samowitsch/raspberry-pi-hq-microscope/pics/pcb/pcb-back.jpg

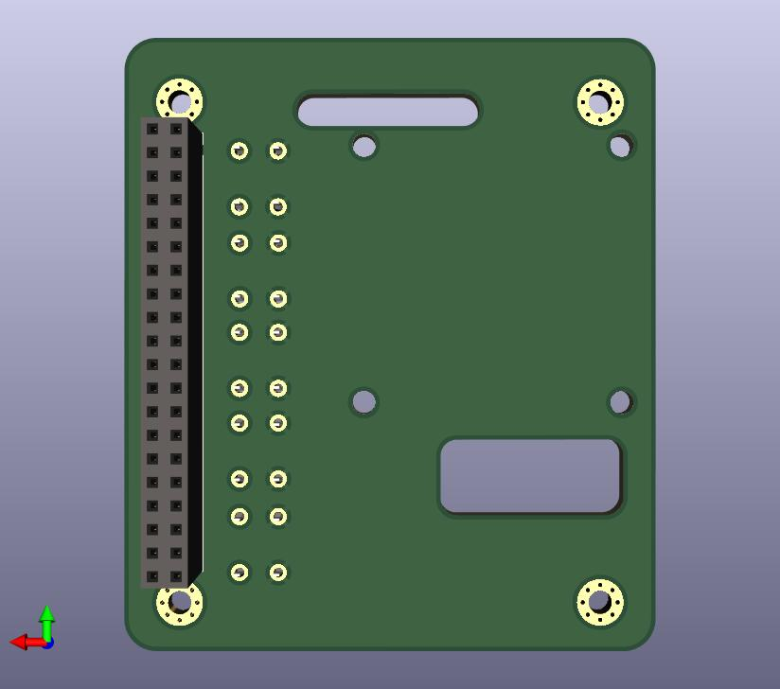
pics/pcb/pcb-back.jpg
