samowitsch/raspberry-pi-hq-microscope/pics/pcb/pcb-front.jpg

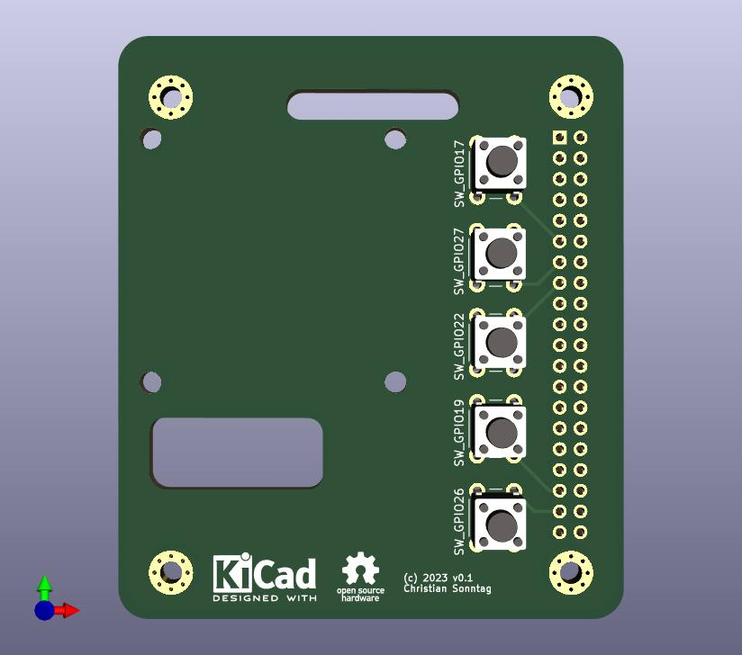
pics/pcb/pcb-front.jpg
