samowitsch/raspberry-pi-hq-microscope/scans/scan-rpi-3a+-case-1-1.png

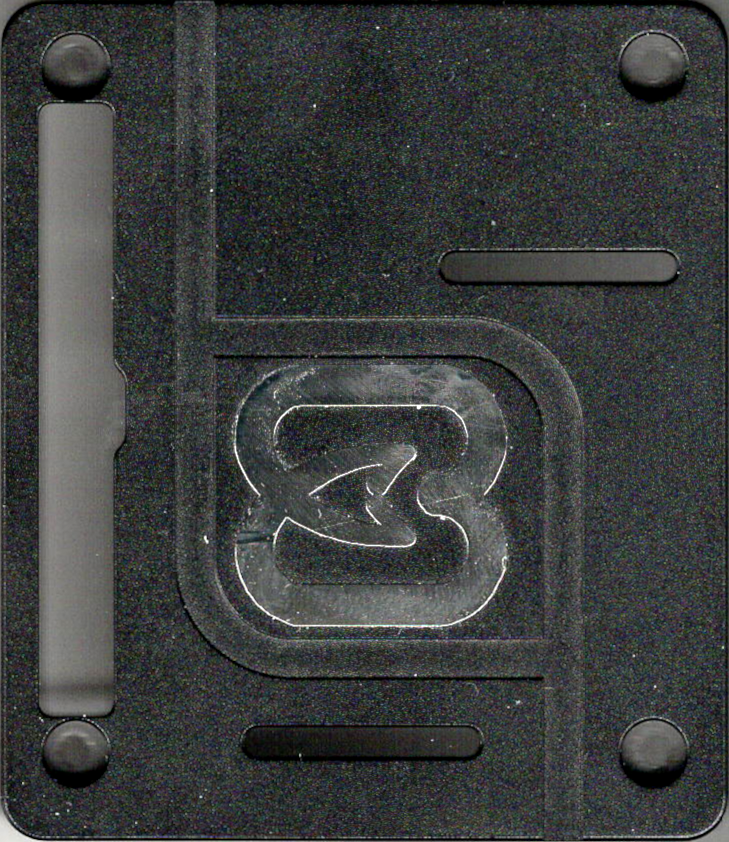
scans/scan-rpi-3a+-case-1-1.png
