samowitsch/raspberry-pi-hq-microscope/scans/scan-rpi-hq-camera-1-1.png

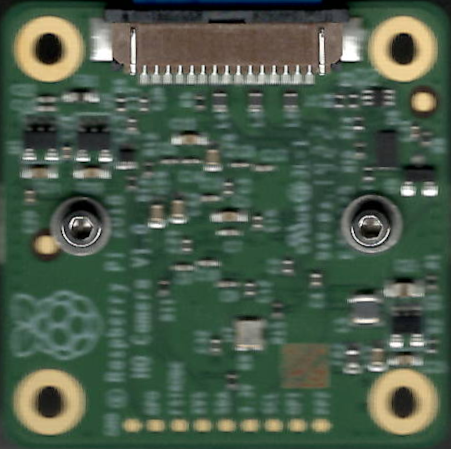
scans/scan-rpi-hq-camera-1-1.png
