samowitsch/raspberry-pi-hq-microscope/pics/bom/edimax-usb-wifi.jpg

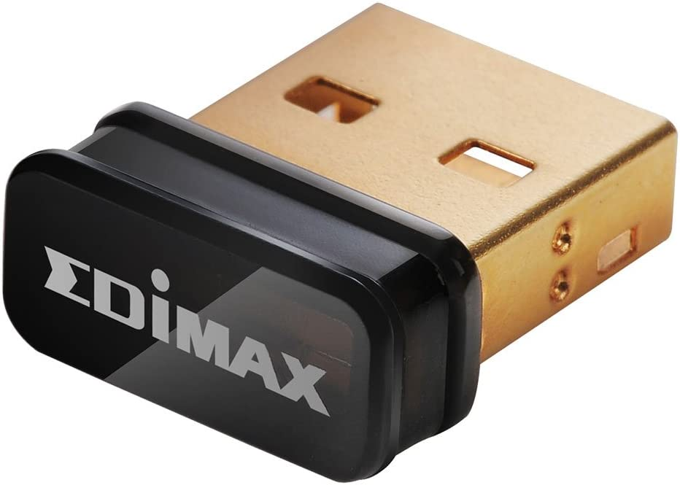
pics/bom/edimax-usb-wifi.jpg
