samowitsch/raspberry-pi-hq-microscope/pics/bom/geekworm-rpi-3a-plus-case.jpg

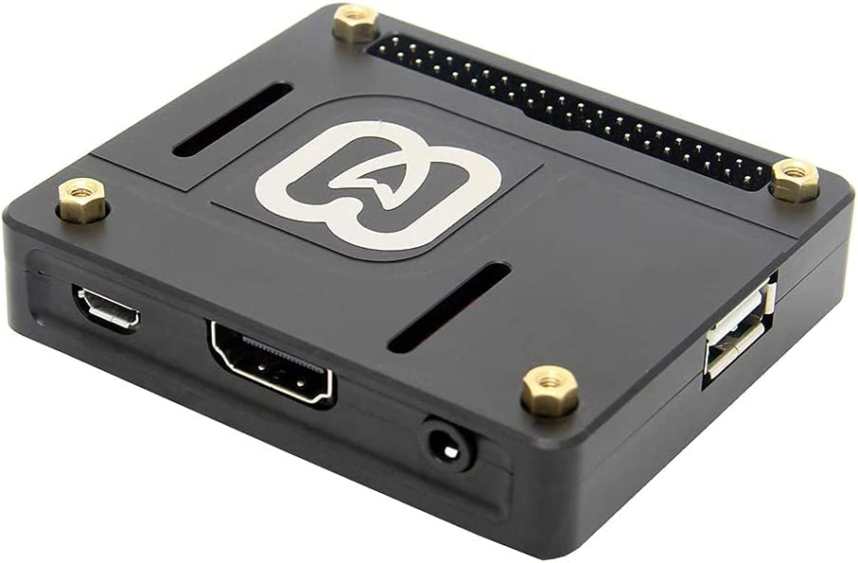
pics/bom/geekworm-rpi-3a-plus-case.jpg
