samowitsch/raspberry-pi-hq-microscope/pics/bom/led-ring-light.jpg

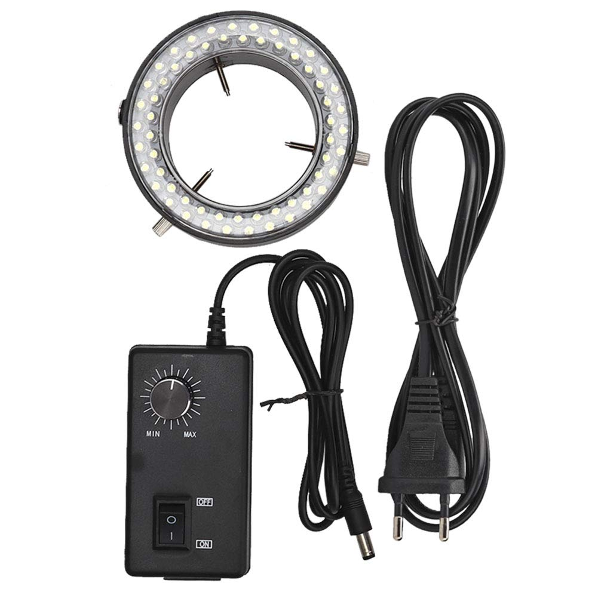
pics/bom/led-ring-light.jpg
