samowitsch/raspberry-pi-hq-microscope/pics/bom/push-button.jpg

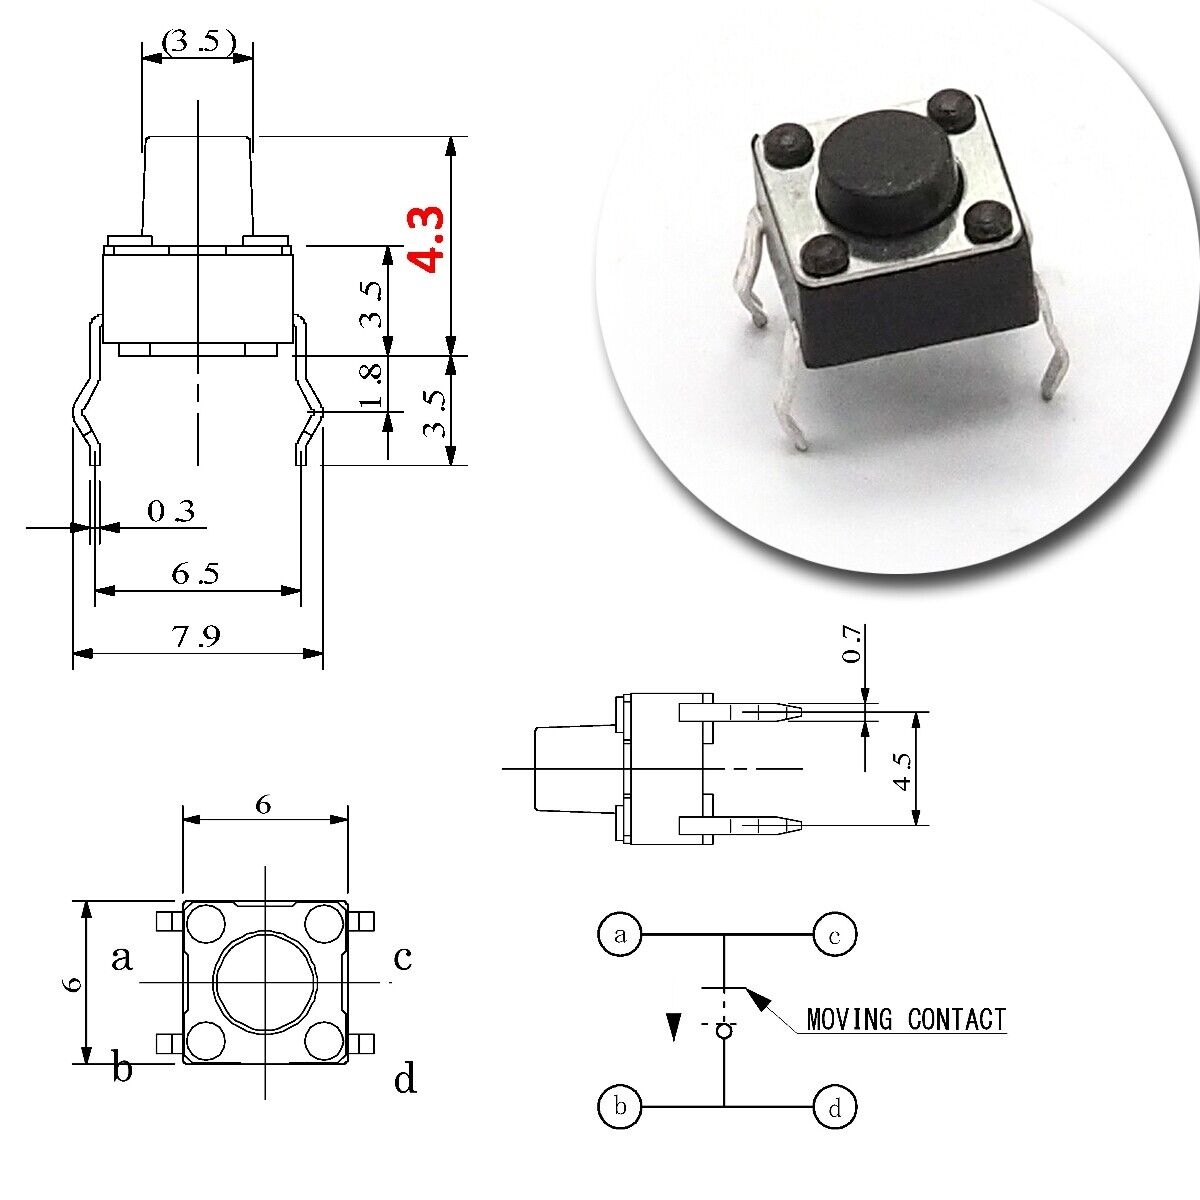
pics/bom/push-button.jpg
