samowitsch/raspberry-pi-hq-microscope/pics/bom/rpi-3a-plus.png

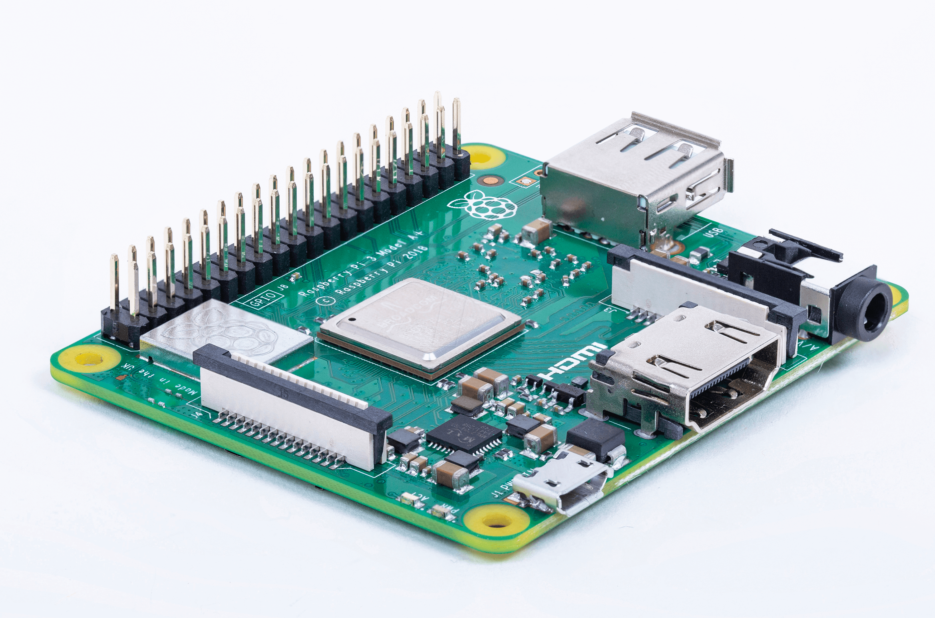
pics/bom/rpi-3a-plus.png
