samowitsch/raspberry-pi-hq-microscope/pics/bom/rpi-camera-cable.jpg

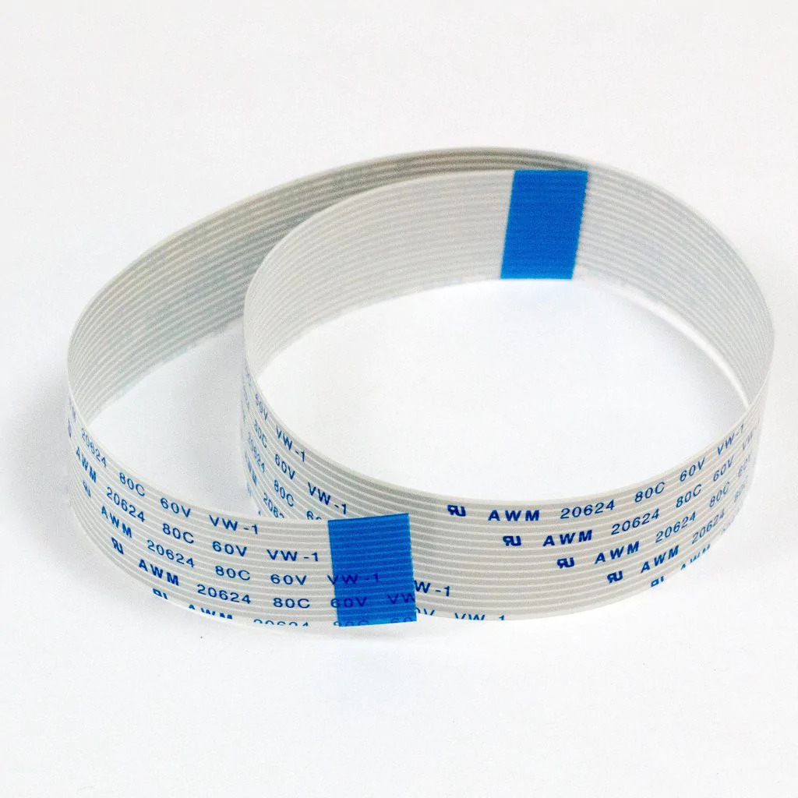
pics/bom/rpi-camera-cable.jpg
